rjafari44/Ultrasonic_Rover/ltspice/rover_schematic.asc

C1: cap; 470µ
X1: arduino_nano
X2: l298n
X3: servoMotor
X4: ultrasonicSensor
Named nets: Bat_8V, 5V_nano, D10, D11, 0, D9, D3, D4, D5, D6, D7, D8, TT_Motor1, TT_Motor2, ENA, IN1, IN2, IN3, IN4, ENB, PWM, TRIG, ECHO, x
Servo
Ultrasonic Sensor
Motor Driver
Microcontroller
